rh1tech/protea/3D/PJ320D.STEP

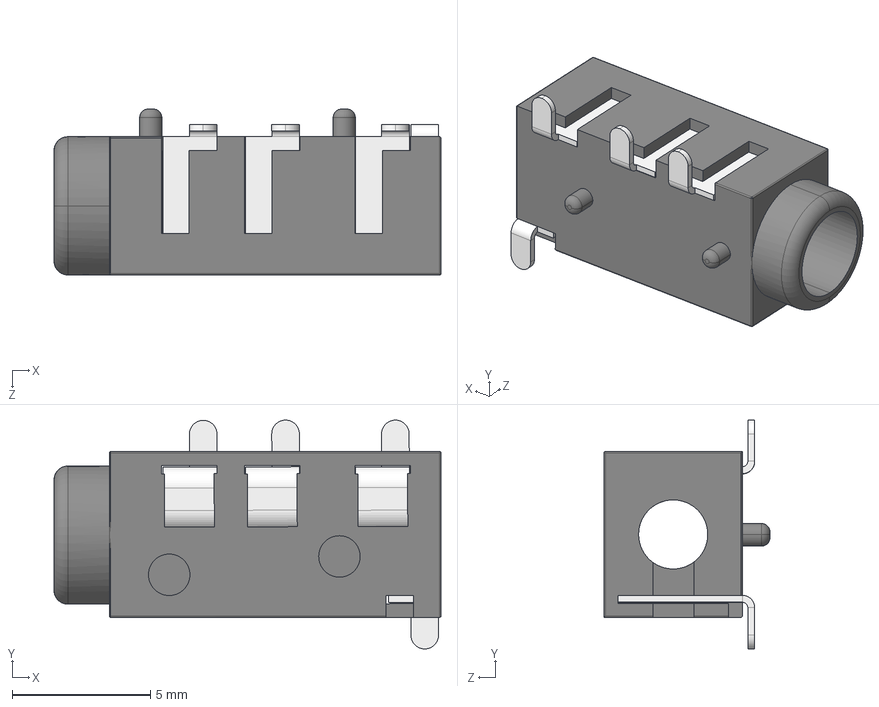
[picture p17: CAD file, 2025-06-26]
3D/PJ320D.STEP
14.0 x 8.28 x 6.00 mm
PJ320A
PJ320D-Pin x 3
PJ320D-Pin-B
