rh1tech/protea/3D/DSUB-9_Female_Horizontal_P2.77x2.84mm_EdgePinOffset9.90mm_Housed_MountingHolesOffset11.32mm.step

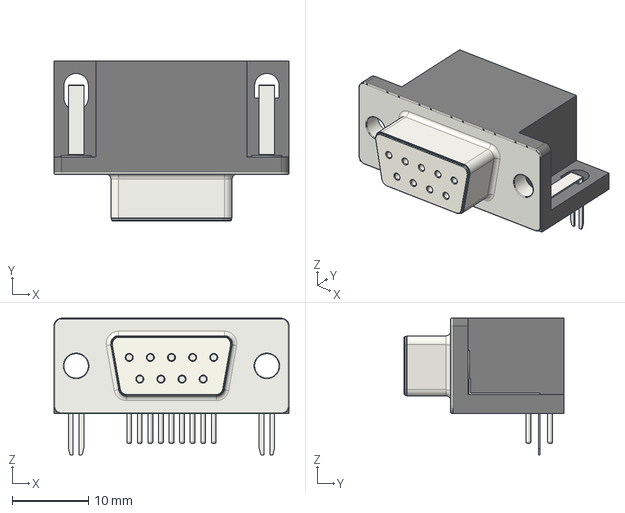
[picture p18: CAD file, 2025-06-26]
3D/DSUB-9_Female_Horizontal_P2.77x2.84mm_EdgePinOffset9.90mm_Housed_MountingHolesOffset11.32mm.step
30.8 x 20.9 x 17.9 mm
