rh1tech/protea/3D/SO-8_5.3x6.2mm_P1.27mm.step

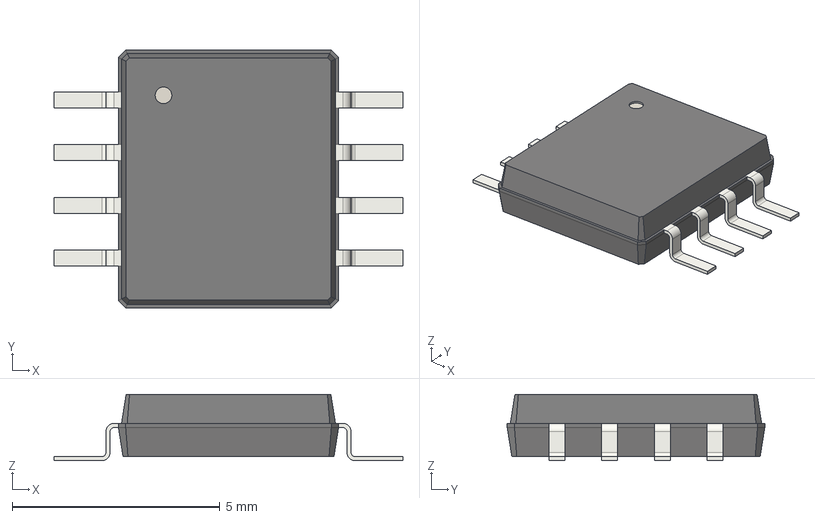
[picture p19: CAD file, 2025-06-26]
3D/SO-8_5.3x6.2mm_P1.27mm.step
8.40 x 6.20 x 1.60 mm
