rh1tech/protea/3D/TS3USB221RSER.stp

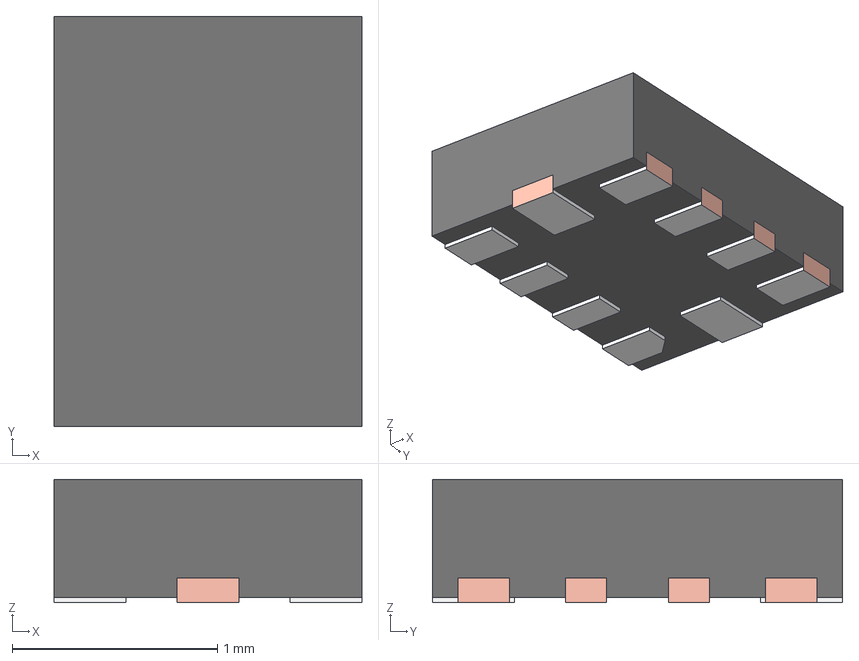
[picture p20: CAD file, 2025-06-26]
3D/TS3USB221RSER.stp
1.50 x 2.00 x 0.6 mm
FRAME-RSE0010A
BODY-QFN
PIN1-ID
