rh1tech/protea/3D/USB1035-GF-P-0-B-B.stp

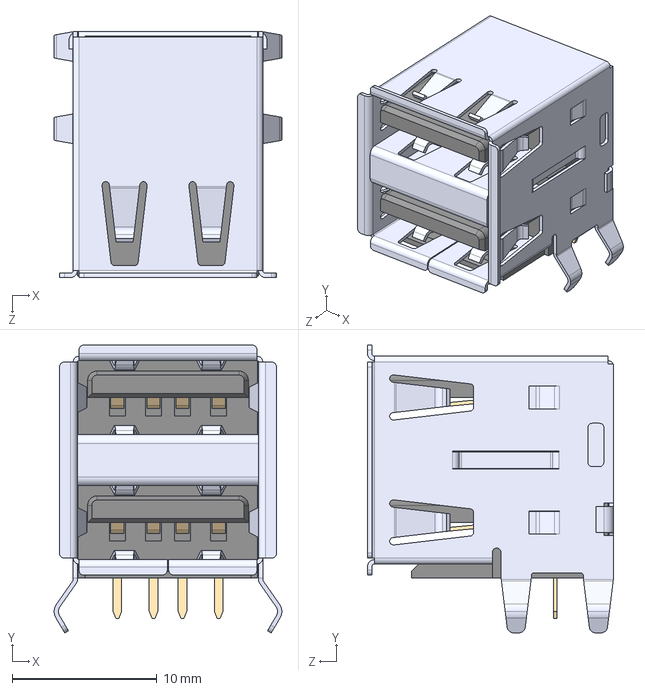
[picture p22: CAD file, 2025-06-26]
3D/USB1035-GF-P-0-B-B.stp
15.7 x 19.9 x 17.0 mm
