rh1tech/protea/3D/CUI_DEVICES_RCJ-013.step

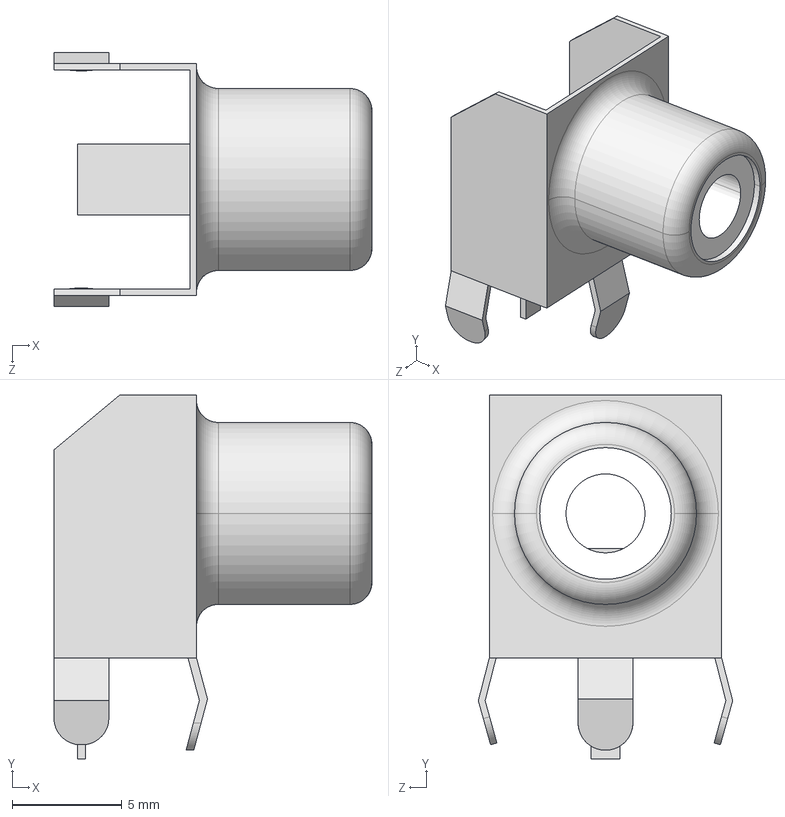
[picture p23: CAD file, 2025-06-26]
3D/CUI_DEVICES_RCJ-013.step
14.5 x 16.6 x 11.6 mm
